MechLabEngineering/Low-Budget-Car-PC-Case/Renderings/Rendering003.png

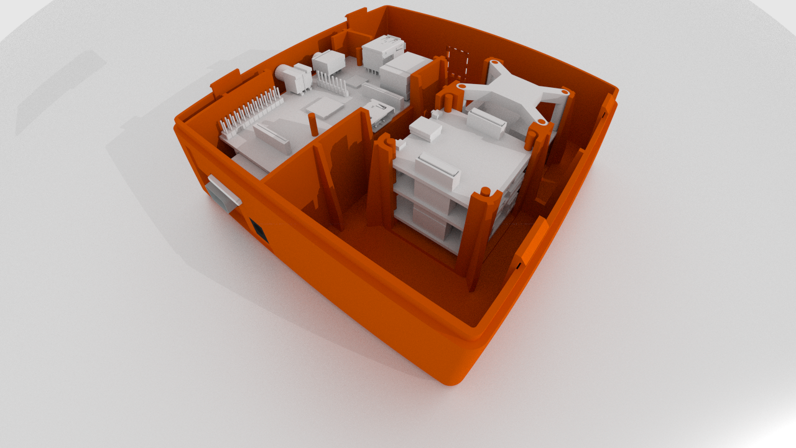
Renderings/Rendering003.png
