MechLabEngineering/Low-Budget-Car-PC-Case/Renderings/Rendering004.png

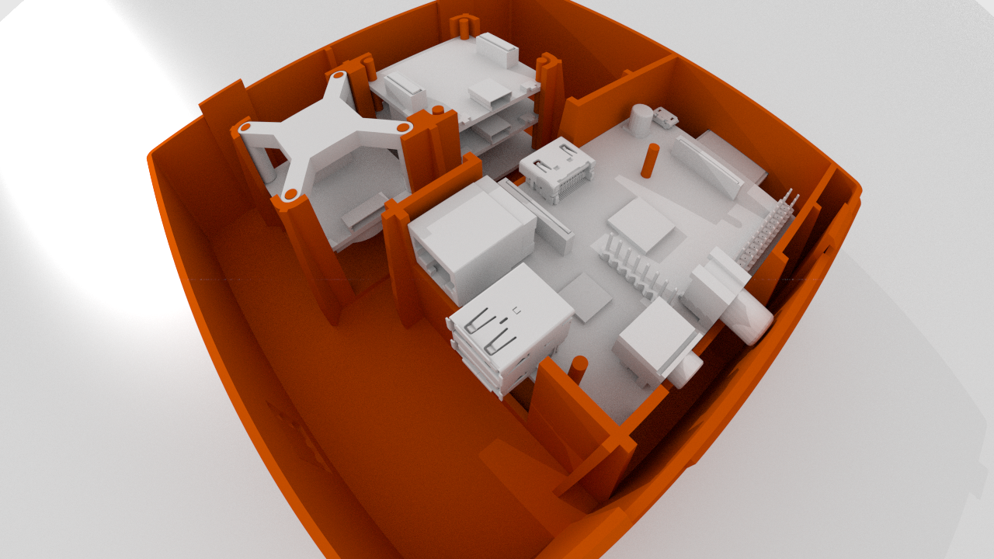
Renderings/Rendering004.png
