MechLabEngineering/Low-Budget-Car-PC-Case/STL-Dateien/CarPC_Case.png

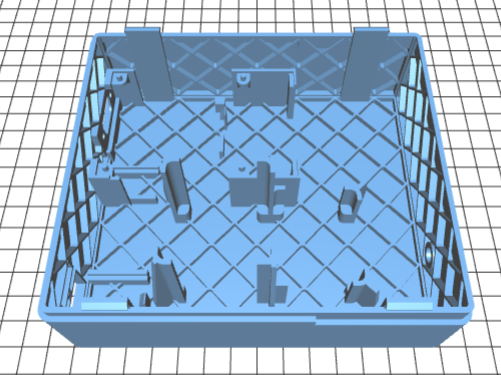
STL-Dateien/CarPC_Case.png
