MechLabEngineering/Low-Budget-Car-PC-Case/STL-Dateien/CarPC_Deckel.png

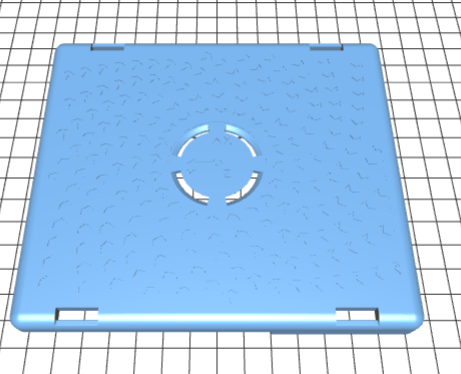
STL-Dateien/CarPC_Deckel.png
