MechLabEngineering/Low-Budget-Car-PC-Case/STL-Dateien/Deckel_render.png

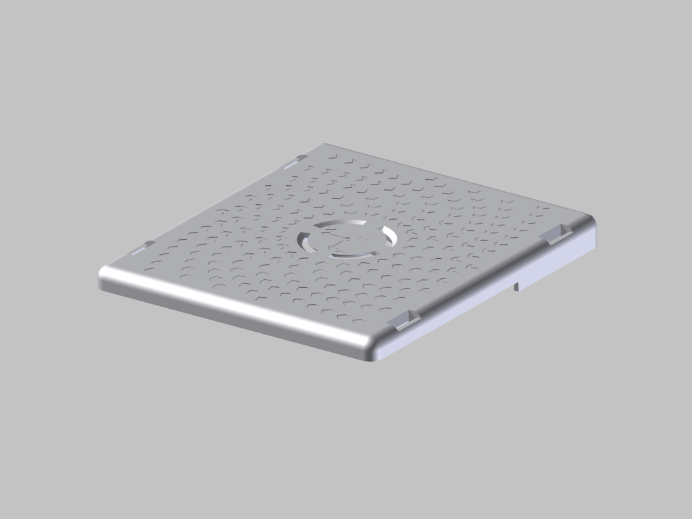
STL-Dateien/Deckel_render.png
