MechLabEngineering/Low-Budget-Car-PC-Case/STL-Dateien/GPS_STL.PNG

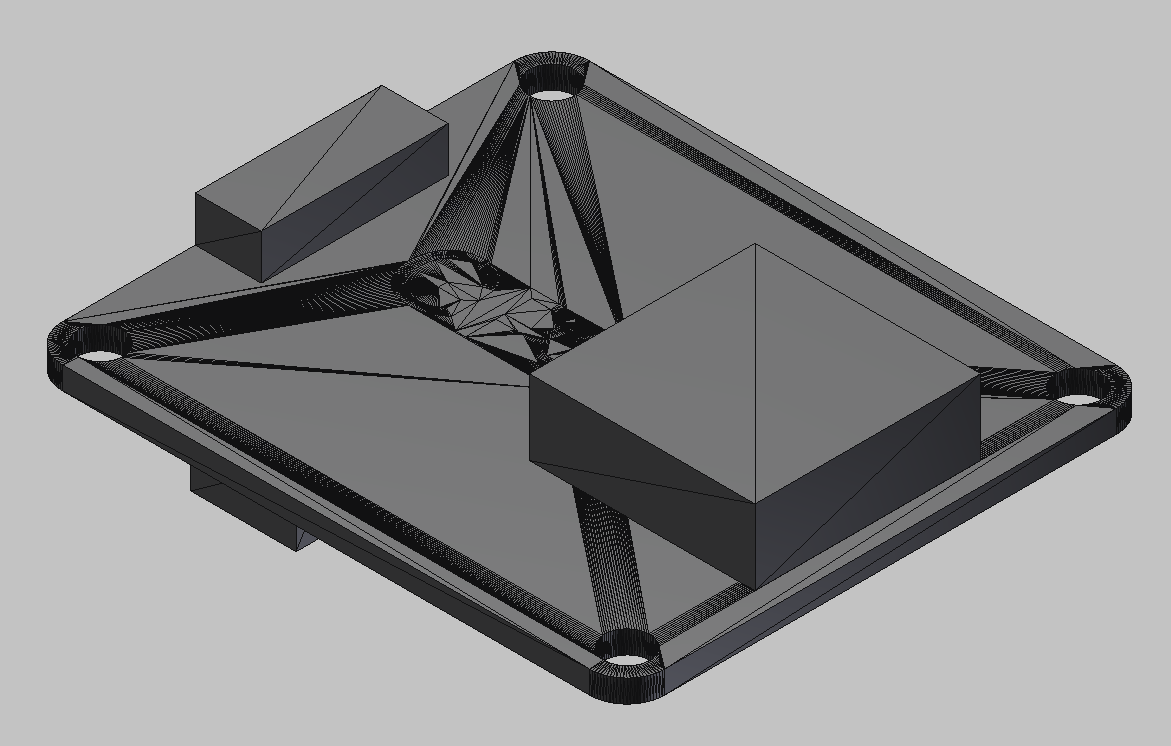
STL-Dateien/GPS_STL.PNG
