MechLabEngineering/Low-Budget-Car-PC-Case/STL-Dateien/Grundbox_V3.2_render.png

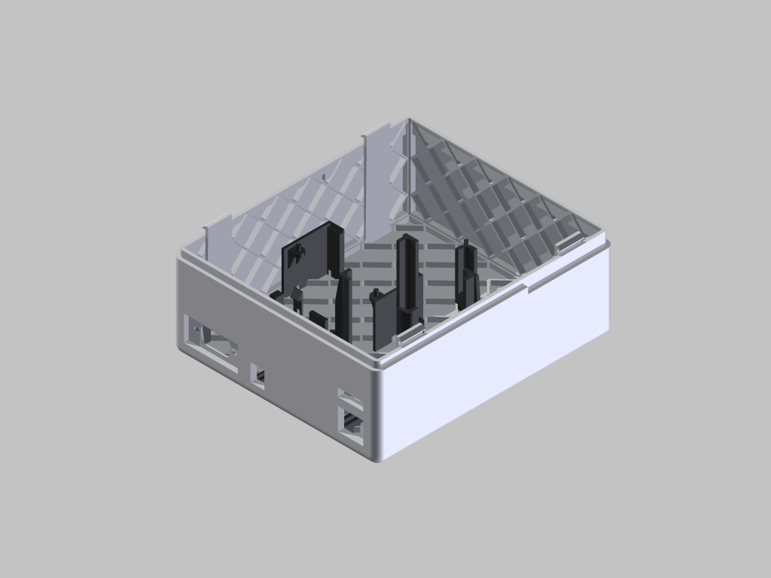
STL-Dateien/Grundbox_V3.2_render.png
