MechLabEngineering/Low-Budget-Car-PC-Case/STL-Dateien/IMU_STL.PNG

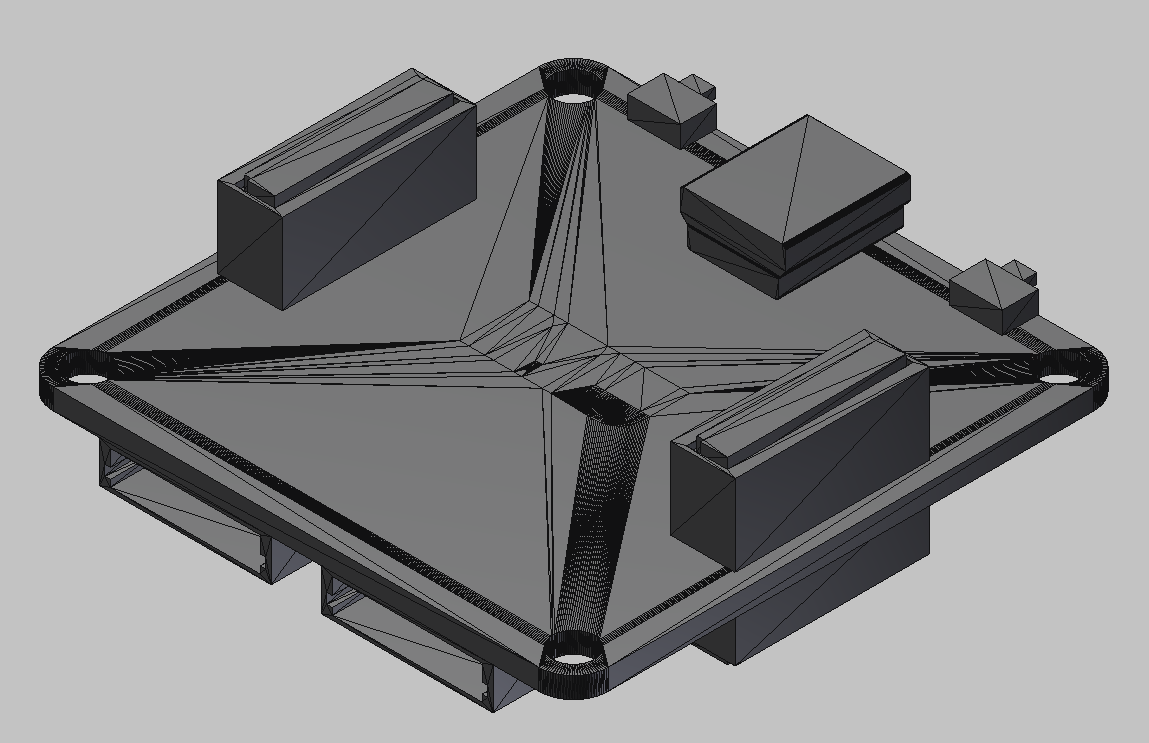
STL-Dateien/IMU_STL.PNG
