MechLabEngineering/Low-Budget-Car-PC-Case/STL-Dateien/TF_Stapel_Power_Master_IMU_STL.PNG

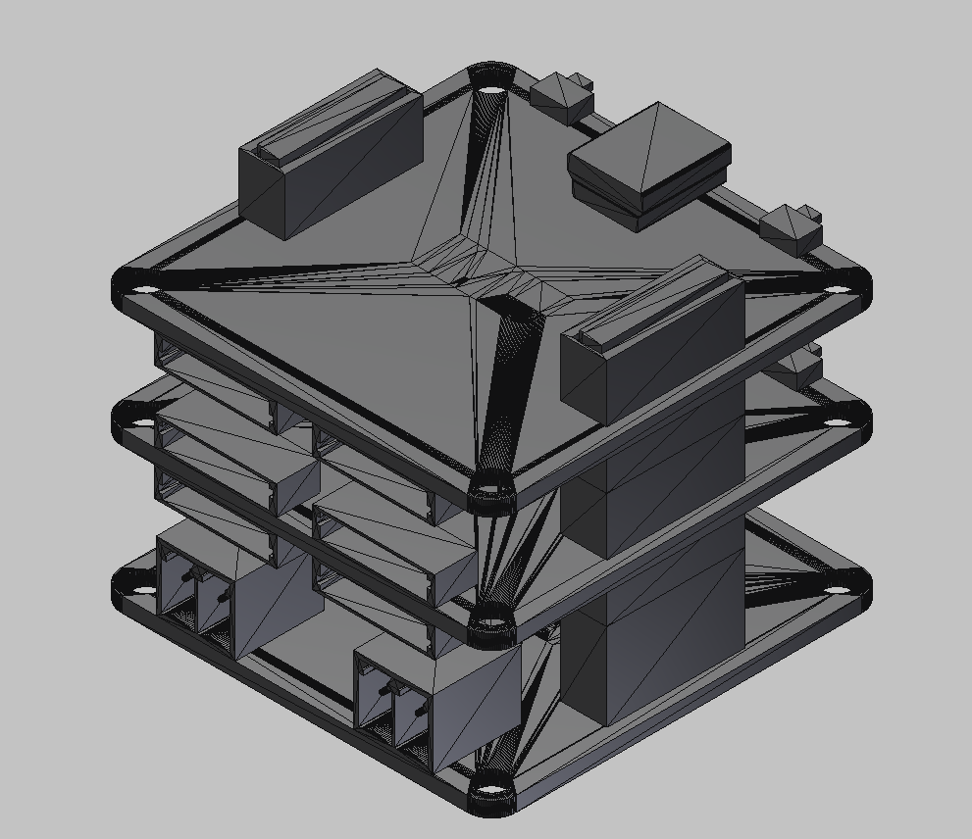
STL-Dateien/TF_Stapel_Power_Master_IMU_STL.PNG
